jdimauro/witch-lights/animations/5_Follow-Through-and-Overlapping.gif

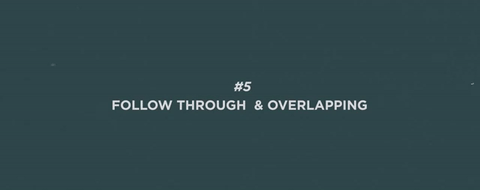
animations/5_Follow-Through-and-Overlapping.gif
