jdimauro/witch-lights/animations/9_Timing.gif

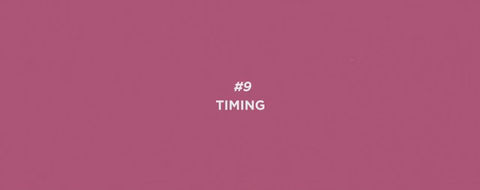
animations/9_Timing.gif
