jdimauro/witch-lights/animations/powershell-output_redacted.jpg

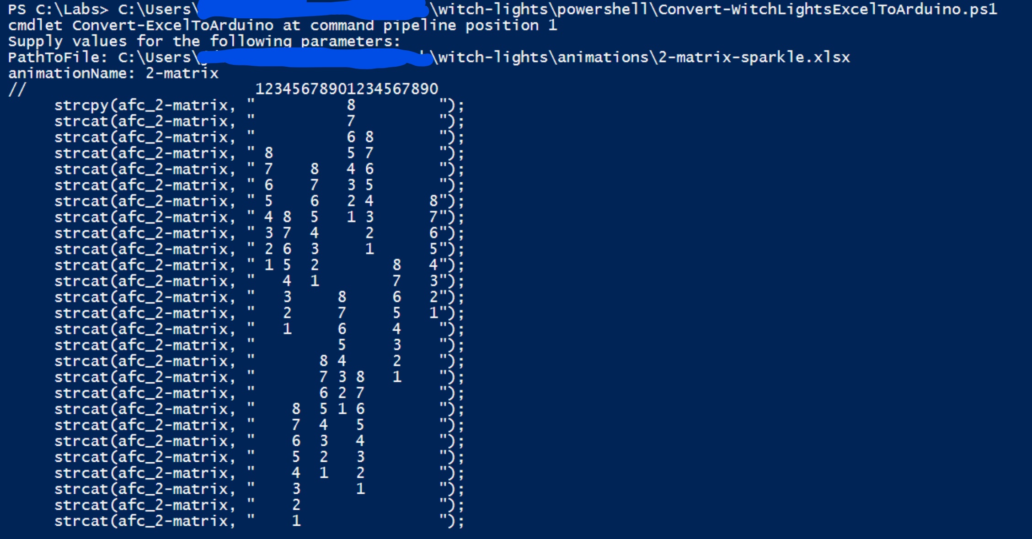
animations/powershell-output_redacted.jpg
