jdimauro/witch-lights/docs/2014-07-04--wl-anim-poc-vt-firefly2014.gif

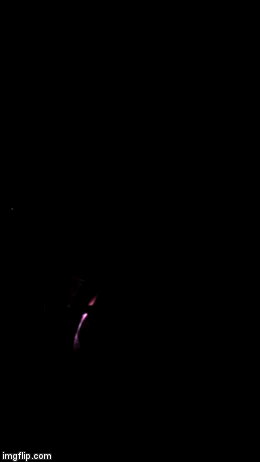
docs/2014-07-04--wl-anim-poc-vt-firefly2014.gif
