jdimauro/witch-lights/docs/2019-01-25--wl-anim-co-boulder.gif

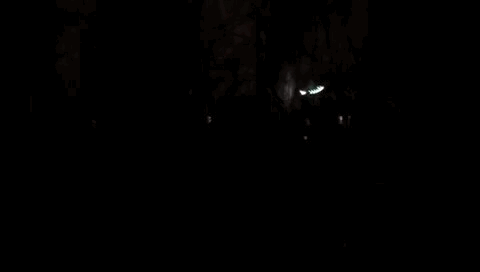
docs/2019-01-25--wl-anim-co-boulder.gif
