jdimauro/witch-lights/docs/2019-01-29--wl-anim-ct-v1.gif

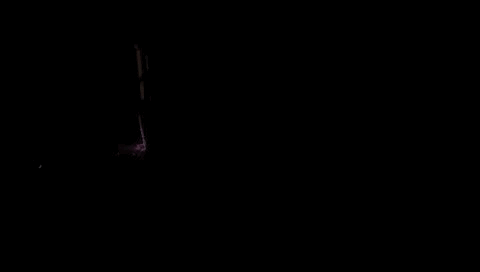
docs/2019-01-29--wl-anim-ct-v1.gif
