jdimauro/witch-lights/docs/2019-07-31--wl-journey-map.jpg

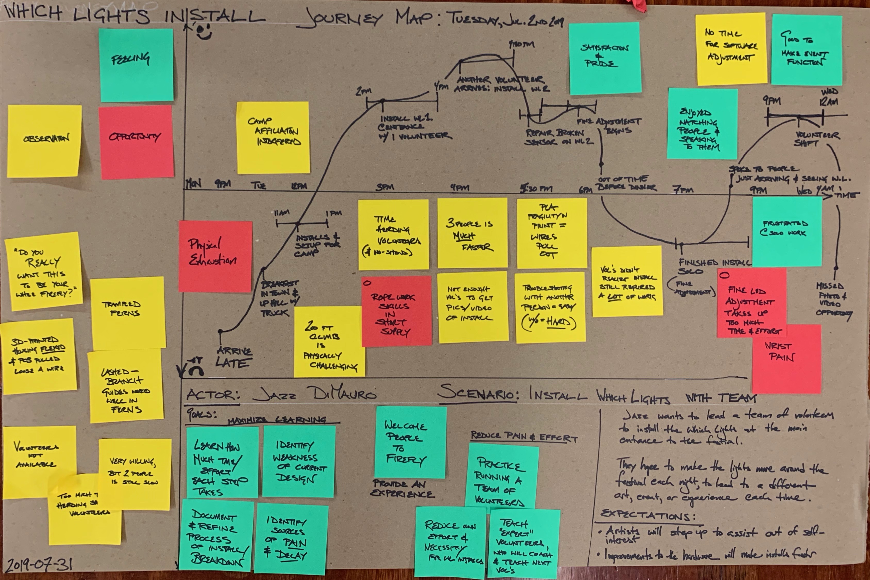
docs/2019-07-31--wl-journey-map.jpg
