jdimauro/witch-lights/docs/wl-ard-enclosure1.jpg

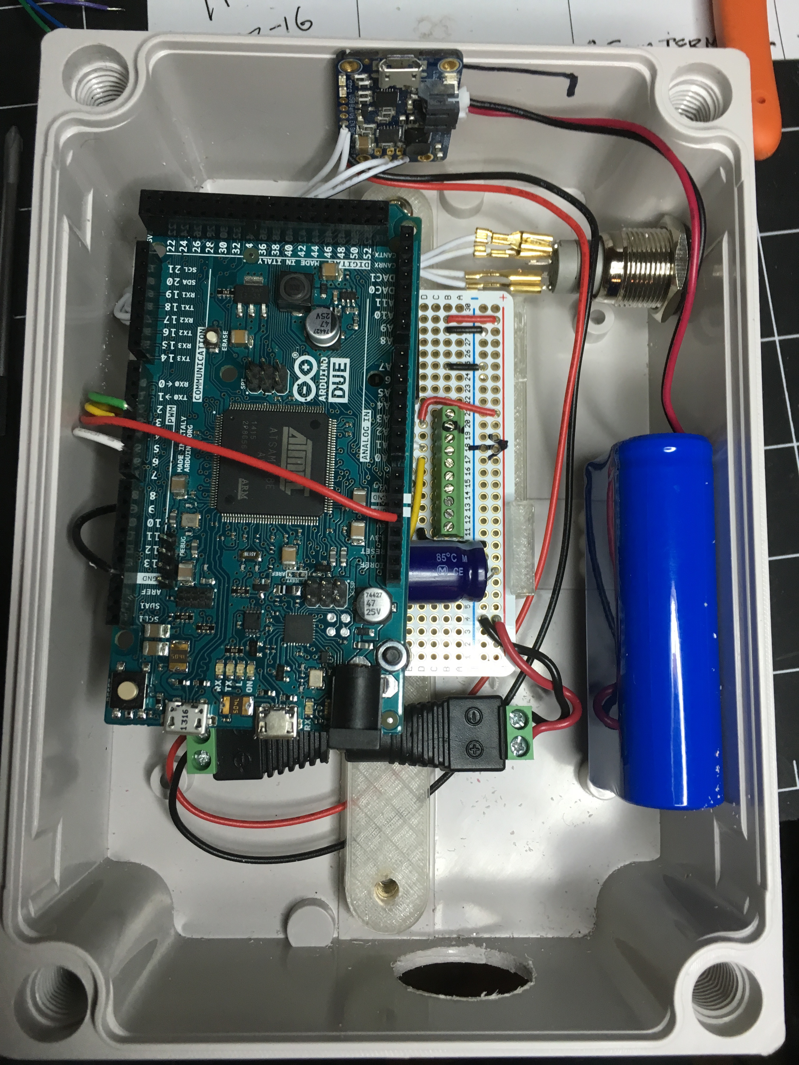
docs/wl-ard-enclosure1.jpg
