jdimauro/witch-lights/docs/wl-ard-proto4.jpg

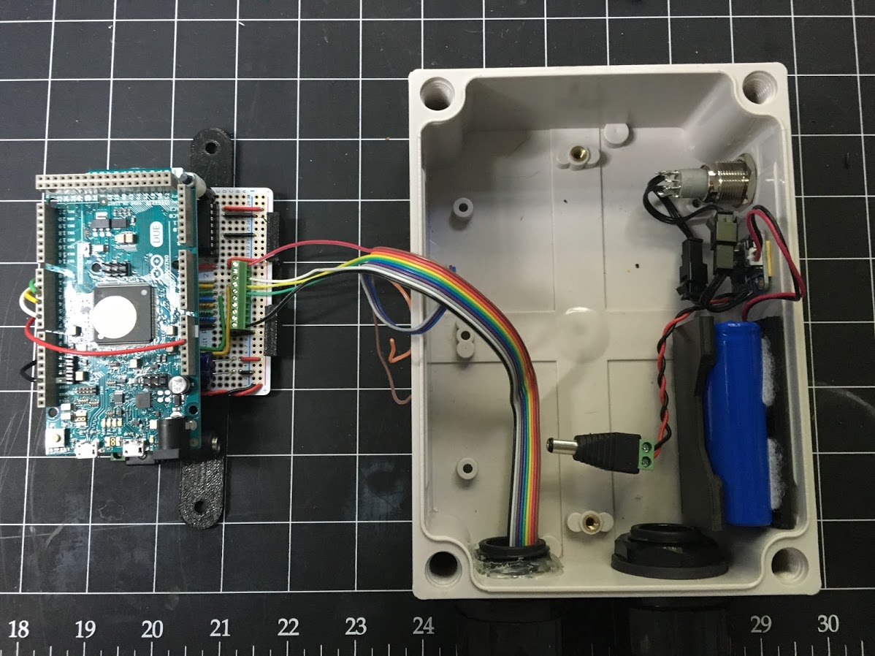
docs/wl-ard-proto4.jpg
