jdimauro/witch-lights/docs/wl-pir-enclosure0.png

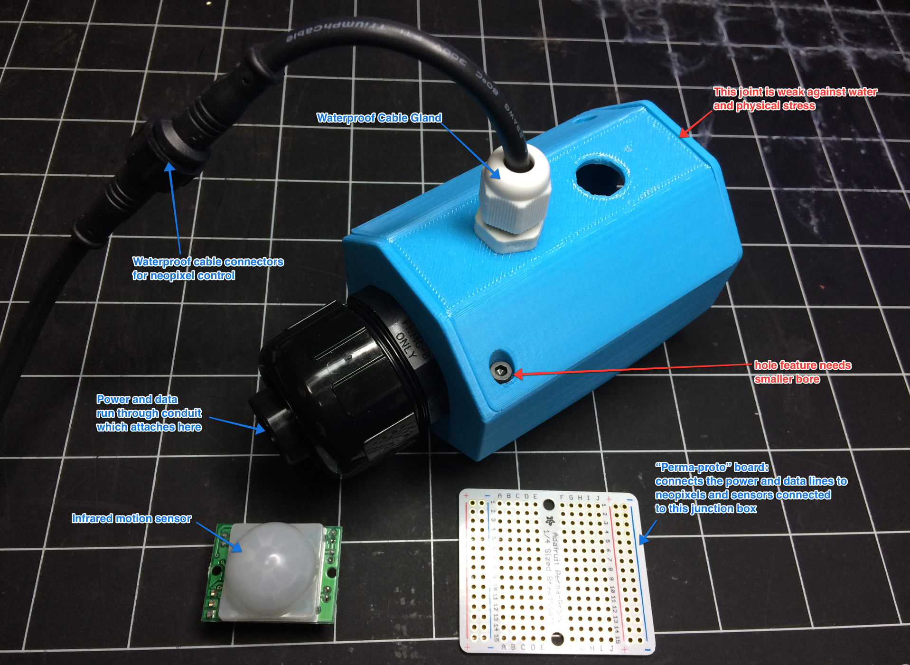
docs/wl-pir-enclosure0.png
