jdimauro/witch-lights/sketches/TreeSprite.png

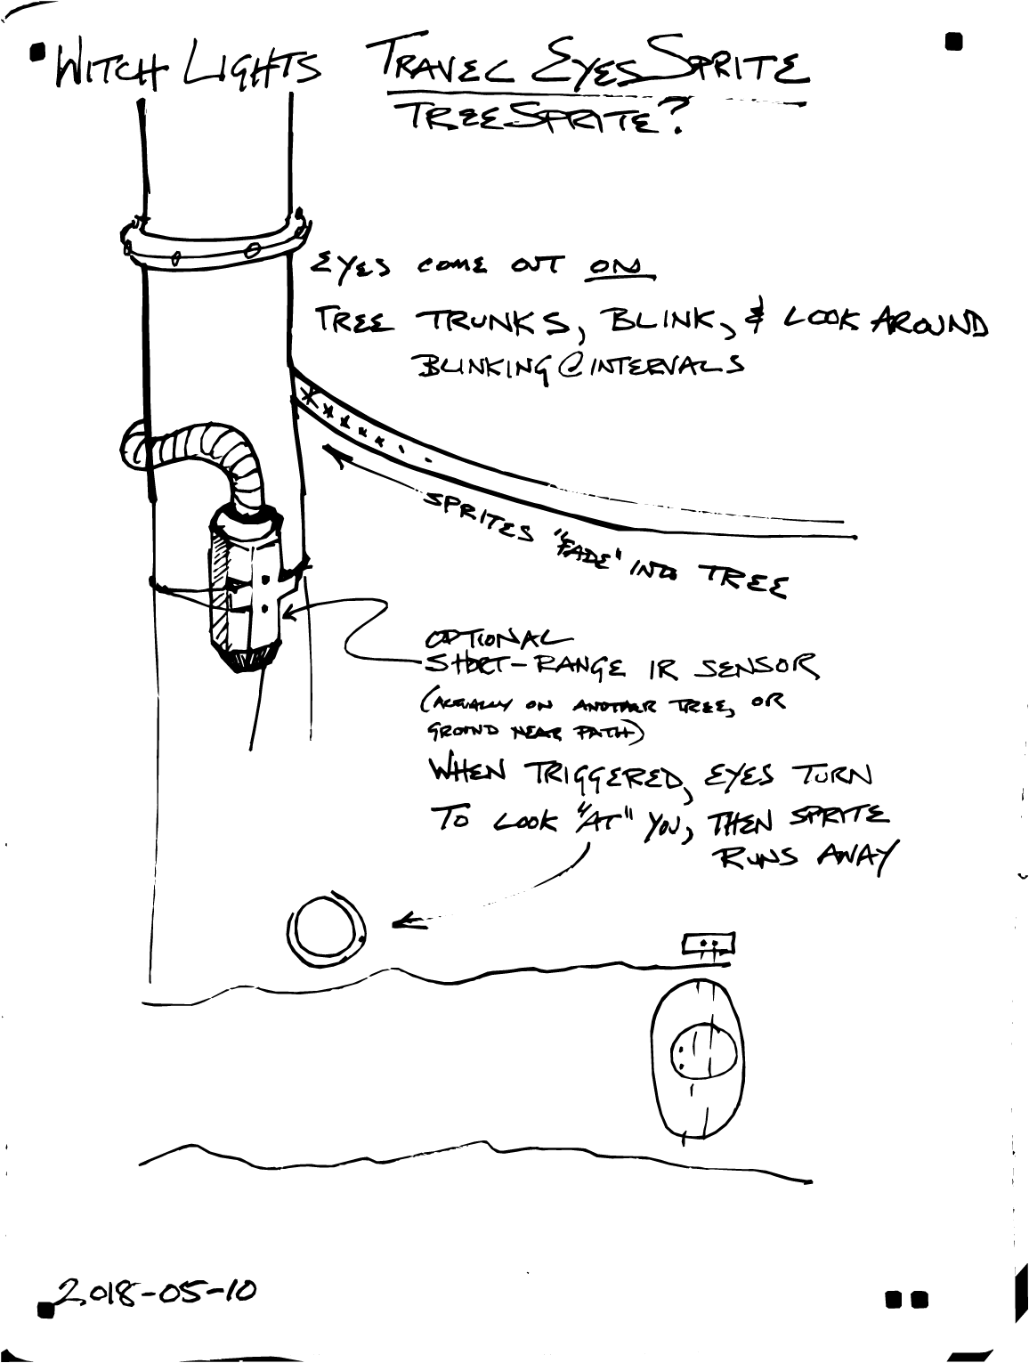
sketches/TreeSprite.png
