jdimauro/witch-lights/twitch/Twitch Scene-Offline-leftalign.png

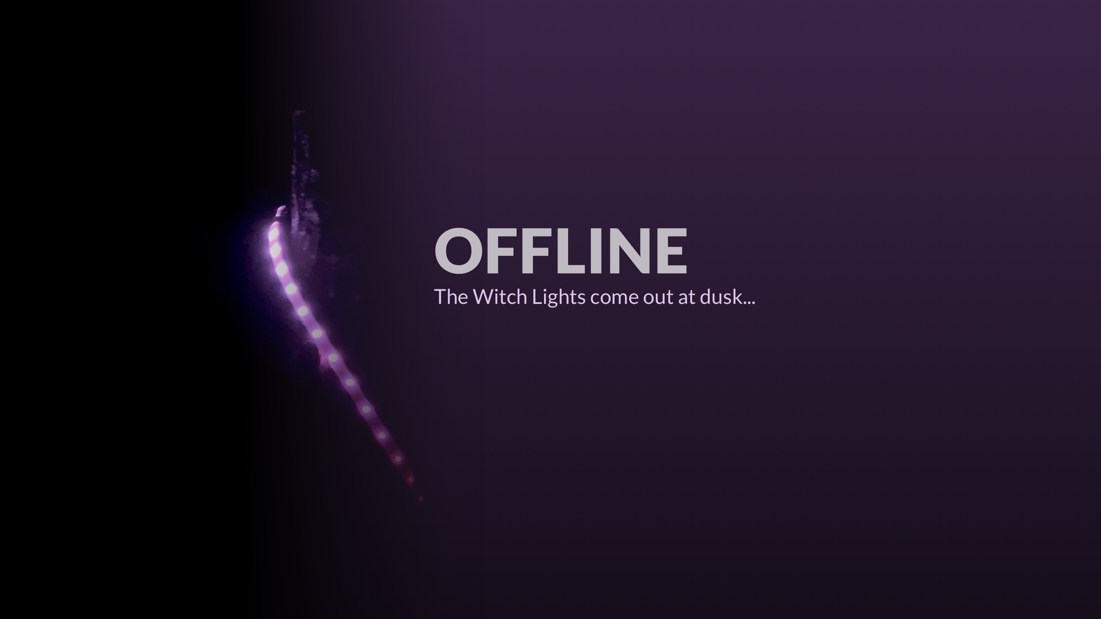
twitch/Twitch Scene-Offline-leftalign.png
