jdimauro/witch-lights/twitch/Twitch Scene-Offline.png

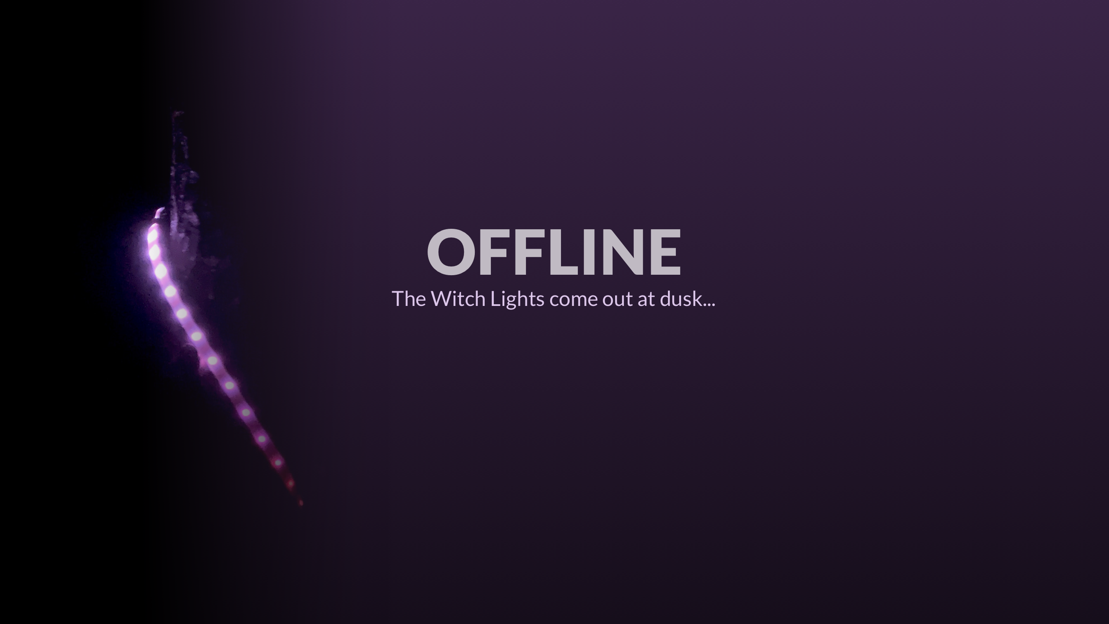
twitch/Twitch Scene-Offline.png
