jdimauro/witch-lights/twitch/Twitch Scene-Standby-Start-leftalign.png

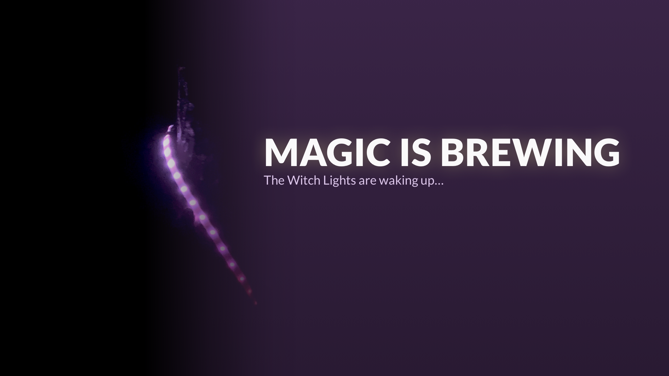
twitch/Twitch Scene-Standby-Start-leftalign.png
