jdimauro/witch-lights/twitch/Twitch Scene-Standby.png

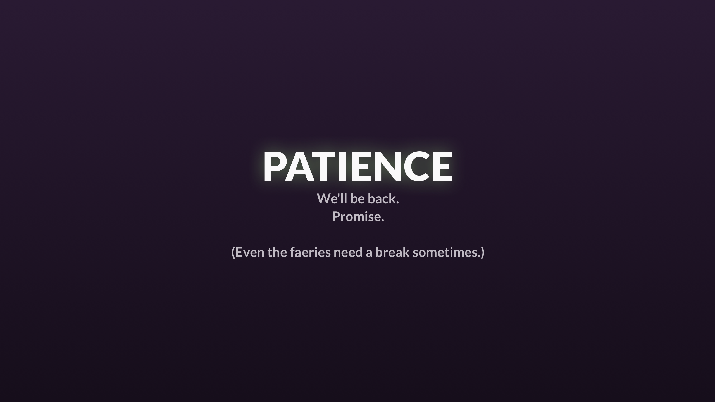
twitch/Twitch Scene-Standby.png
