jdimauro/witch-lights/animations/3-pulse-arduino.ino

//                        123456789012345678901234567890123456789012345678901234567890123456789012345678901234567
     strcpy(afc_3_pulse, "       88                                                                              ");
     strcat(afc_3_pulse, "       88                                                                              ");
     strcat(afc_3_pulse, "       77                                                                              ");
     strcat(afc_3_pulse, "       66                                                                              ");
     strcat(afc_3_pulse, "       55                                                                              ");
     strcat(afc_3_pulse, "       44                                                                              ");
     strcat(afc_3_pulse, "       44                                                                              ");
     strcat(afc_3_pulse, "       44                                                                              ");
     strcat(afc_3_pulse, "       55                                                                              ");
     strcat(afc_3_pulse, "       66                                                                              ");
     strcat(afc_3_pulse, "       77                                                                              ");
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
     strcat(afc_3_pulse, "       881                                                                             ");
     strcat(afc_3_pulse, "       88                                                                              ");
