jdimauro/witch-lights/arduino/witchlights-fastled/wifiauth-example.cpp

#include "wifiauth.h"

// Enter the ssid and password for your wifi, rename this file to 'wifiauth.cpp', and uncomment the following lines:

// const char* ssid = "...........";
// const char* password = "...........";
